podonoghue/T962a_Oven_Controller/Software/SMT_Oven_stubs/Project_Headers/USBDM_Documentation.h

/**
 * @file     USBDM_Documentation.h (180.ARM_Peripherals/Project_Headers/USBDM_Documentation.h)
 * @brief    USBDM Documentation
 */
 
 /**
 @mainpage USBDM Overview

 The classes in the USBDM namespace provide C++ wrappers for the microcontroller hardware. \n

\tableofcontents
Table of Contents
 - \ref ADCExamples \n
 - \ref Console \n
 - \ref DMAExamples \n
 - \ref FTMExamples \n
 - \ref GPIOExamples \n
 - \ref I2CExamples \n
 - \ref LPTMRExamples \n
 - \ref PDBExamples \n
 - \ref PinSummary  \n
 - \ref PITExamples \n
 - \ref SPIExamples \n

@page I2CExamples  I2C interface

Convenience template for SPI. Uses the following classes:\n
<ul>
<li>USBDM::I2cBase_T < Info >
<li>USBDM::I2c
<ul>
<li>USBDM::I2c0
<li>USBDM::I2c1
</ul>
</ul>

<b>Examples</b>\n
 - @ref i2c-example.cpp

@page SPIExamples  SPI interface

Convenience template for SPI. Uses the following classes:\n
<ul>
<li>USBDM::SpiBase_T < Info >
<li>USBDM::Spi
<ul>
<li>USBDM::Spi0
<li>USBDM::Spi1
</ul>
</ul>

<b>Examples</b>\n
 - @ref spi-example.cpp

@page Console  Console and UART interface

Convenience template for UART. Uses the following classes:\n
<ul>
<li>USBDM::Uart_T < Info >
<li>USBDM::UartBuffered_T < Info, rxSize, txSize >
<ul>
<li>USBDM::Console
<li>USBDM::Uart0
<li>USBDM::Uart1
<li>USBDM::Uart2
</ul>
</ul>

<b>Examples</b>\n
 - @ref console-example.cpp

<b>Usage</b>
 @code

   console.writeln("Hello World");

   int value;
   console.write("Enter value: ").readln(value);
   console.write("Value =").writeln(value);

   console<<"Enter value: ">>value<<EndOfLine;
   console<<"Value ="<<value<<EndOfLine;

   // I/O with error checks
   if (console.write("Number: ").readln(integer).isError()) {
      console.writeln("Opps");
   }
   else {
      console.writeln(integer);
   }

   // Utility functions
   Console::ultoa(100, buff);
   console.write("ultoa(100, buff)  = ").writeln(buff);
   Console::ltoa(-100, buff);
   console.write("ltoa(-100, buff)  = ").writeln(buff);

   char *ptr = buff;
   ptr = Console::strcpy(ptr, "Console::ultoa(100, buff) = ");
   ptr = Console::ultoa(100, ptr);
   ptr = Console::strcpy(ptr, ", oh well!");
   console.writeln(buff);
 @endcode

@page DMAExamples  Direct Memory Access Controller

Convenience template for DMAC. Uses the following classes:\n
<ul>
<li>USBDM::DmaTcd \n
<li>USBDM::DmaMux_T < DmaMuxInfo > \n
<li>USBDM::DmaBase_T < DmaInfo > \n
</ul>

This template is an interface for the Direct Memory Access Controller hardware. \n

It provides:\n
- Definitions for channel mappings
- Methods to configure the DMAC and DMAMUX

This is a template class with static methods.\n
<em>It cannot be instantiated.</em>

<b>Examples</b>\n
 - @ref dma-memory-example.cpp
 - @ref dma-memory-template-example.cpp
 - @ref dma-spi-example.cpp
 - @ref dma-uart-example-mk20.cpp
 - @ref dma-uart-example-mk22f.cpp
 - @ref dma-uart-example-mk28f.cpp

 @page GPIOExamples  General Purpose Input Output

@page LPTMRExamples  Low Power Timer

Convenience template for LPTMR. Uses the following classes:\n
<ul>
<li>USBDM::LptmrBase_T < Info > \n
</ul>

This template is an interface for the Low Power Timer hardware. \n

It provides:\n
- Static pin mapping in conjunction with the configuration settings.

This is a template class with static methods.\n
<em>It cannot be instantiated.</em>

<b>Examples</b>\n
 - @ref lptmr-example.cpp
 
 @page GPIOExamples  General Purpose Input Output

Convenience template for GPIO pins. Uses the following classes:\n
<ul>
<li>USBDM::GpioBase_T &lt;clockMask, portAddress, gpioAddress, bitNum, polarity&gt; \n
<li>USBDM::Gpio_T &lt;Info, bitNum, polarity&gt;\n
<ul>
<li>USBDM::GpioA &lt;bitNum, polarity&gt;
<li>USBDM::GpioB &lt;bitNum, polarity&gt;
<li>USBDM::GpioC &lt;bitNum, polarity&gt;
<li>USBDM::GpioD &lt;bitNum, polarity&gt;
<li>USBDM::GpioE &lt;bitNum, polarity&gt;
</ul>
<li>USBDM::Field_T &lt;Info, left, right, polarity&gt;\n
<ul>
<li>USBDM::GpioAField &lt;left, right, polarity&gt;
<li>USBDM::GpioBField &lt;left, right, polarity&gt;
<li>USBDM::GpioCField &lt;left, right, polarity&gt;
<li>USBDM::GpioDField &lt;left, right, polarity&gt;
<li>USBDM::GpioEField &lt;left, right, polarity&gt;
</ul>
</ul>

This template is an interface for the general purpose I/O pin hardware. \n

It provides:\n
- Static pin mapping in conjunction with the configuration settings.
- Setting pin characteristics e.g. pull-ups, drive strength etc
- Changing the pin direction
- Setting outputs to high or low level
- Polling input value
- Polarity (\ref USBDM::ActiveHigh or \ref USBDM::ActiveLow) is selected when instantiated

This is a template class with static methods.\n
<em>It cannot be instantiated.</em>

<b>Examples</b>\n
 - @ref digital-example1.cpp
 - @ref digital-example2.cpp

<b>Usage</b>
 @code
   // Open USBDM namespace.
   // This allows access to USBDM classes and methods without the USBDM:: prefix.
   using namespace USBDM;

   // Temporary for input values
   bool x;

   // Use pin 3 of PORTC as active-high GPIO i.e. PTC3
   using Gpio = GpioC<3, ActiveHigh>;

   // Set as digital output
   Gpio::setOutput();
   // or for more detailed control
   Gpio::setOutput(PinDriveStrength_High, PinDriveMode_OpenDrain);

   // Set pin to active level (polarity is applied)
   Gpio::setActive();
   // or
   Gpio::on();

   // Clear pin to inactive level (polarity is applied)
   Gpio::setInactive();
   // or
   Gpio::off();

   // Set pin to a high level (polarity is ignored)
   Gpio::set();
   // or
   Gpio::high();

   // Set pin to a low level (polarity is ignored)
   Gpio::clear();
   // or
   Gpio::low();

   // Toggle pin
   Gpio::toggle();

   // Set pin to boolean value (polarity is applied)
   Gpio::write(true);

   // Set pin to boolean value (polarity is applied)
   Gpio::write(false);

   // Enable pull-up
   // This will only have effect when pin is an input
   Gpio::setPullDevice(PinPull_Up);

   // Set drive strength
   Gpio::setDriveStrength(PinDriveStrength_High);

   // Set open-drain
   Gpio::setDriveMode(PinDriveMode_OpenDrain);

   // Read pin as boolean value (polarity is applied)
   x = Gpio::read();

   // Read _state_ of pin drive as boolean value (polarity is applied)
   // This may differ from the value on the pin
   // May be useful if the pin is open-drain
   Gpio::setDriveMode(PinOpenDrain);
   Gpio::high();
   if (Gpio::readState() != Gpio::read()) {
      console.writeln("Open-drain pin is being held low");
   }

   // Dynamically change pin to input
   Gpio::setIn();

   // Read pin as boolean value (polarity is applied)
   x = Gpio::read();

   // Read pin as boolean value (polarity is ignored)
   x = Gpio::isHigh();

   // Read pin as boolean value (polarity is ignored)
   x = Gpio::isLow();
 @endcode

@page ADCExamples Analogue-to-Digital

Convenience template for ADC inputs. Use the following classes:\n
<ul>
<li>USBDM::AdcBase_T
<ul>
<li>USBDM::Adc0
<li>USBDM::Adc1
</ul>
<li>USBDM::AdcChannel_T
<ul>
<li>USBDM::Adc0Channel
<li>USBDM::Adc1Channel
</ul>
<li>USBDM::AdcDiffChannel_T
<ul>
<li>USBDM::Adc0DiffChannel
<li>USBDM::Adc1DiffChannel
</ul>
</ul>
This template is an interface for the ADC input pins. \n

It provides:\n
- Static pin mapping in conjunction with the configuration settings. (Some ADC pins have fixed mapping.)
- Setting the resolution in bits
- Setting the conversion parameters e.g. averaging
- Clock and conversion speed are done through the configuration.
- Interrupt driven operation is also supported through a callback if enabled in the configuration.

This is a template class with static methods.\n
<em>It cannot be instantiated.</em>

<b>Examples</b>\n
 - @ref analogue-comparison-example.cpp
 - @ref analogue-diff-example.cpp
 - @ref analogue-interrupt-example.cpp
 - @ref analogue-joystick-example.cpp

 <b>Usage - Single-ended measurement</b>
 @code
   // Open USBDM namespace.
   // This allows access to USBDM classes and methods without the USBDM:: prefix.
   using namespace USBDM;

   // ADC being used (for shared settings)
   using Adc         = Adc0;

   // Use ADC0 channel 6 as ADC input (ADC_IN6)
   using AdcChannel = USBDM::Adc0Channel<6>;

   // Initially configure ADC for resolution of 16 bits with default settings
   Adc::configure(AdcResolution_16bit_se);

   // Calibrate before use
   Adc::calibrate();
   
   // Set ADC averaging to 4 samples
   Adc::setAveraging(AdcAveraging_4);

   // Read ADC value
   uint32_t value = AdcChannel::readAnalogue();

   console.write("ADC measurement = ").writeln(value);
 @endcode

 <b>Usage - Differential measurement</b>
 @code
   // Open USBDM namespace.
   // This allows access to USBDM classes and methods without the USBDM:: prefix.
   using namespace USBDM;

   // ADC being used (for shared settings)
   using Adc         = Adc0;

   // Use channel 0 as ADC differential input (ADC_DM0, ADC_DP0)
   using Adc1_diff0 = USBDM::Adc0DiffChannel<0>;

   // Initially configure ADC for resolution of 11 bits differential with default settings
   Adc::configure(AdcResolution_11bit_diff);

   // Calibrate before use
   Adc::calibrate();
   
   // Set ADC averaging to 4 samples
   Adc::setAveraging(AdcAveraging_4);

   // Read signed differential ADC value
   int32_t value = Adc1_diff0::readAnalogue();

   console.write("ADC measurement = ").writeln(value);
 @endcode

@page FTMExamples Flexible Timer Module

Convenience template for FTM hardware.
The interface is divided into a number of templates:
<ul>
<li>USBDM::FtmBase_T Representing the shared FTM functionality.
<ul>
<li>USBDM::Ftm0
<li>USBDM::Ftm1
</ul>
<li>USBDM::QuadEncoder_T Representing a FTM operating as a quadrature encoder.
<ul>
<li>USBDM::QuadEncoder1
</ul>
<li>USBDM::FtmChannel_T Representing individual channels of a single FTM.
<ul>
<li>USBDM::Ftm0Channel
<li>USBDM::Ftm1Channel
</ul>
</ul>
It provides:\n
<ul>
<li>Static pin mapping in conjunction with the configuration settings.
<li>Setting the FTM period in ticks or seconds
<li>Setting the channel duty cycle in percentage
<li>Interrupt driven operation is also supported through a callback if <b>enabled in the configuration</b>.
</ul>

This is a template class with static methods.\n
<em>It cannot be instantiated.</em>

<b>Examples</b>\n
 - @ref ftm-ic-example.cpp
 - @ref ftm-oc-example.cpp
 - @ref ftm-pwm-example.cpp
 - @ref ftm-quadrature-example.cpp
 - @ref ftm-servo-example.cpp

 <b>Usage - PWM</b>
@code
   // Open USBDM namespace.
   // This allows access to USBDM classes and methods without the USBDM:: prefix.
   using namespace USBDM;

   // Initialise the timer with initial alignment
   // This affects all channels of the FTM
   Ftm0::configure(FtmMode_LeftAlign);

   // Set timer period in ticks
   // This affects all channels of the FTM
   // Timer pre-scaler is not changed
   Ftm0::setPeriodInTicks(500);

   // Set timer period in microseconds
   // This affects all channels of the FTM
   // Timer pre-scaler (tick rate) will be adjusted to accommodate the required period
   Ftm0::setPeriod(125*us);

   // Use FTM0 channel 3
   using PwmOutput = Ftm0Channel<3> ;

   // Set channel to generate PWM with active-high pulses
   PwmOutput::enable(ftm_pwmHighTruePulses);

   // Set duty cycle as percentage
   PwmOutput::setDutyCycle(34);

   // Set duty cycle as percentage (float)
   PwmOutput::setDutyCycle(12.25*percent);

   // Set high time in microseconds (float)
   PwmOutput::setHighTime(63*us);
@endcode

 <b>Usage - Quadrature Encoder</b>
@code
   // Open USBDM namespace.
   // This allows access to USBDM classes and methods without the USBDM:: prefix.
   using namespace USBDM;

   // Use FTM1 as the quadrature encoder
   // Not all FTMs support this mode
   using QuadEncoder = QuadEncoder1;

   // Enable encoder
   QuadEncoder::enable();

   // Set pin filters
   QuadEncoder::enableFilter(15);

   // Reset position to zero
   // Movement will be relative to this position
   QuadEncoder::resetPosition();

   // Set up callback for quadrature overflow or underflow
   QuadEncoder::setTimerOverflowCallback(callBack);
   QuadEncoder::enableTimerOverflowInterrupts();
   QuadEncoder::enableNvicInterrupts();

   for (;;) {
      // Report position
      console.write("Shaft position = ").writeln(QuadEncoder::getPosition());
   }
@endcode

@page PITExamples Programmable Interrupt Timer Module

Convenience template for PIT hardware. \n
Uses the following classes:
<ul>
<li> USBDM::PitBase_T &lt;Info&gt;
<li> USBDM::Pit
<li> USBDM::PitChannel &lt;channel&gt;
</ul>
It provides:\n
- Static pin mapping in conjunction with the configuration settings.
- Setting the PIT channel period in seconds
- Accurate busy-wait delays using a timer channel
- Interrupt driven operation is also supported through a callback if enabled in the configuration.

This is a template class with static methods.\n
<em>It cannot be instantiated.</em>

<b>Examples</b>\n
 - @ref pit-example1.cpp
 - @ref pit-example2.cpp
 - @ref pit-example3.cpp

<b>Usage - PIT busy-wait</b>
@code
   // Open USBDM namespace.
   // This allows access to USBDM classes and methods without the USBDM:: prefix.
   using namespace USBDM;

   // LED is assumed active-low
   using Led = GpioA<2, ActiveLow>;

   // Use high drive for LED
   Led::setOutput(pcrValue(PinPull_None, PinDrive_High));

   // Enable PIT
   Pit::enable();

   // Check for errors so far
   checkError();

   for(;;) {
      Led::toggle();

      // Delay in milliseconds using channel 0
      Pit::delay(0, 1000*ms);
   }
@endcode

@page PDBExamples Programmable Delay Block Module

Convenience template for PDB hardware. Based on USBDM::PdbBase_T.\n

It provides:\n
- PDB configuration

This is a template class with static methods.\n
<em>It cannot be instantiated.</em>

<b>Examples</b>\n
 - @ref pdb-example.cpp

<b>Usage - PDB Software Trigger</b>
@code
   // Open USBDM namespace.
   // This allows access to USBDM classes and methods without the USBDM:: prefix.
   using namespace USBDM;

   Pdb::enable();
   // Trigger from FTM
   Pdb::setTriggerSource(PdbTrigger_Software);
   // Set callback
   Pdb::setCallback(pdbCallback);
   // Interrupt during sequence
   Pdb::enableSequenceInterrupts();
   // Set period a bit longer than FTM period
   Pdb::setPeriod(PERIOD);
   // Generate interrupt near end of sequence
   Pdb::setInterruptDelay(PERIOD-5*ms);
   // Take ADC samples before and after sample edge
   Pdb::setPretriggers(0, PdbPretrigger0_Delayed, HIGH_TIME-SAMPLE_DELAY, PdbPretrigger1_Delayed, HIGH_TIME+SAMPLE_DELAY);
   // Update registers
   Pdb::triggerRegisterLoad(PdbLoadMode_immediate);

   Pdb::enableNvicInterrupts();

   Pdb::softwareTrigger();
@endcode

@page Notes Notes
  - enable()            Enables clock and configures pins (if any configured in Configure.usbdmProject)
  - configureAllPins()  Configures all pins associated with the peripheral
  - defaultConfigure()  enable() + initialises according to Configure.usbdmProject\n
                        May have defaulted parameters to do custom configuration.
  - disable()           Disables the peripheral

@example analogue-comparison-example.cpp
@example analogue-diff-example.cpp
@example analogue-interrupt-example.cpp
@example analogue-joystick-example.cpp
@example cmp-example.cpp
@example console-example.cpp
@example dac-example.cpp
@example digital-example1.cpp
@example digital-example2.cpp
@example dma-memory-example.cpp
@example dma-memory-template-example.cpp
@example dma-spi-example.cpp
@example dma-uart-example-mk20.cpp
@example dma-uart-example-mk22f.cpp
@example dma-uart-example-mk28f.cpp
@example flash_programming_example.cpp
@example ftm-ic-example.cpp
@example ftm-oc-example.cpp
@example ftm-pwm-example.cpp
@example ftm-quadrature-example.cpp
@example ftm-servo-example.cpp
@example fxos8700cq-example.cpp
@example fxos8700cq.cpp
@example fxos8700cq.h
@example hmc5883l-example.cpp
@example hmc5883l.cpp
@example hmc5883l.h
@example i2c-example.cpp
@example llwu-example-mk20.cpp
@example llwu-example-mk22f.cpp
@example lptmr-example.cpp
@example mag3310-example.cpp
@example mag3310.cpp
@example mag3310.h
@example mma845x-example.cpp
@example mma845x.cpp
@example mma845x.h
@example mma8491q-example.cpp
@example mma8491q.cpp
@example mma8491q.h
@example nonvolatile_example.cpp
@example pca9685-example.cpp
@example pca9685.cpp
@example pca9685.h
@example pit-example1.cpp
@example pit-example2.cpp
@example pit-example3.cpp
@example pdb-example.cpp
@example rtc-example.cpp
@example spi-example.cpp
@example mcg-test.cpp
@example tsi-mk-example.cpp
@example usb.cpp
@example usb_cdc_interface.cpp
@example usb_cdc_interface.h
@example usb_implementation.h
@example usb_implementation_bulk.cpp
@example usb_implementation_bulk.h
@example usb_implementation_cdc.cpp
@example usb_implementation_cdc.h
@example usb_implementation_composite.cpp
@example usb_implementation_composite.h

 */
