podonoghue/T962a_Oven_Controller/Software/SMT_Oven_RTOS/Project_Headers/cmsis.h

/**
 * @file cmsis.h (180.ARM_Peripherals/Project_Headers/cmsis.h)
 *
 *  Created on: 20Feb.,2017
 *      Author: podonoghue
 */
#ifndef INCLUDE_USBDM_CMSIS_H_
#define INCLUDE_USBDM_CMSIS_H_

#include <cmath>
#include "cmsis_os.h"
#include "error.h"

/**
 * Namespace enclosing wrapper classes for CMSIS-RTX
 */
namespace CMSIS {

/**
 * Set error code
 *
 * @param[in]  err Error code to set
 *
 * @return Error code
 */
inline static USBDM::ErrorCode setCmsisErrorCode(int err) {
   if (err != 0) {
      // Bump error CMSIS error code to avoid conflict with USBDM error codes
      err |= USBDM::E_CMSIS_ERR_OFFSET;
   }
   USBDM::errorCode = (USBDM::ErrorCode)err;
   return USBDM::errorCode;
}

/**
 * Set error code and check for error
 *
 * @param[in]  err Error code to set
 *
 * @return Error code
 */
inline static USBDM::ErrorCode setAndCheckCmsisErrorCode(int err) {
   if (err != 0) {
      // Bump error CMSIS error code to avoid conflict with USBDM error codes
      err |= USBDM::E_CMSIS_ERR_OFFSET;
   }
   USBDM::errorCode = (USBDM::ErrorCode)(err);
   return USBDM::checkError();
}

using Callback = void (*)(const void *);

/**
 * Wrapper for CMSIS Timer
 *
 * A timer allows the scheduling of the execution of a callback function after a particular
 * delay(osTimerOnce mode) or at a regular interval (osTimerPeriodic mode).
 *
 * Example:
 * @code
 * //
 * // Timer example
 * //
 * void timerExample() {
 *    // auto function used as call-backs
 *    static auto cb1 = [] (const void *) {
 *       RED_LED::toggle();
 *    };
 *    static auto cb2 = [] (const void *) {
 *       GREEN_LED::toggle();
 *    };
 *
 *    // Create the two timer being used
 *    static CMSIS::Timer myTimer1(cb1, osTimerPeriodic);
 *    static CMSIS::Timer myTimer2(cb2, osTimerPeriodic);
 *
 *    RED_LED::setOutput();
 *    GREEN_LED::setOutput();
 *
 *    // Start the timers 
 *    myTimer2.start(500);
 *    myTimer1.start(1000);
 *
 *    printf(" myTimer1::getId() = %p\n\r", myTimer1.getId());
 *    printf(" myTimer2::getId() = %p\n\r", myTimer2.getId());
 * }
 * @endcode
 */
class Timer {

private:
   /**
    * Based on os_timer_cb in rt_CMSIS.c
    * Timer Control Block
    */
   struct osTimerControlBlock_t {
      struct os_timer_cb_ *next;   // Pointer to next active Timer
      uint8_t             state;   // Timer State
      uint8_t              type;   // Timer Type (Periodic/One-shot)
      uint16_t         reserved;   // Reserved
      uint32_t             tcnt;   // Timer Delay Count
      uint32_t             icnt;   // Timer Initial Count
      void                 *arg;   // Timer Function Argument
      const osTimerDef_t *timer;   // Pointer to Timer definition
   };

   volatile osTimerControlBlock_t  os_timer_cb  = {0,0,0,0,0,0,0,0};
   const    osTimerDef_t           os_timer_def;

public:
   /**
    * Constructor - Create timer
    *
    * @param[in] callback  Call-back function to execute by timer
    * @param[in] argument  Pointer to data to pass to callback (should be persistent)
    * @param[in] timerType Type of timer e.g. osTimerPeriodic, osTimerOnce
    */
   Timer(Callback callback, void *argument, os_timer_type timerType) :
      os_timer_def{callback, (void*)&os_timer_cb} {
      osTimerId timer_id __attribute__((unused)) = osTimerCreate(&os_timer_def, timerType, argument);
      usbdm_assert((void*)timer_id == (void*)&os_timer_cb, "Internal check failed");
   }
   /**
    * Constructor - Create timer of given type
    *
    * @param[in] callback  Call-back function to execute by timer
    * @param[in] timerType Type of timer e.g. osTimerPeriodic, osTimerOnce
    */
   Timer(Callback callback, os_timer_type timerType) :
      Timer(callback, nullptr, timerType) {
   }
   /**
    * Constructor - Create Periodic timer
    *
    * @param[in] callback  Call-back function to execute by timer
    * @param[in] argument  Pointer to data to pass to callback (should be persistent)
    */
   Timer(Callback callback, void *argument=nullptr) :
      Timer(callback, argument, osTimerPeriodic){
   }
   /**
    * Destructor
    */
   ~Timer() {
      if (os_timer_cb.state != 0) {
         destroy();
      }
   }
   /**
    * Recreate the associated CMSIS timer with different characteristics
    *
    * @param[in] argument  Pointer to data to pass to callback (should be persistent)
    * @param[in] timerType Type of timer e.g. osTimerPeriodic, osTimerOnce
    *
    * @return true  Success
    * @return false Failure
    */
   bool create(void *argument=nullptr, os_timer_type timerType=osTimerPeriodic) {
      if (os_timer_cb.state != 0) {
         osStatus rc = destroy();
         if (rc != osOK) {
            return rc;
         }
      }
      osTimerId timer_id = osTimerCreate(&os_timer_def, timerType, argument);
      return ((void*)timer_id == (void*)&os_timer_cb);
   }
   /**
    * Destroy the associated CMSIS timer
    *
    * @return error code:
    * @return - osOK:              The timer has been deleted.
    * @return - osErrorISR:        Cannot be called from interrupt service routines.
    * @return - osErrorParameter:  Parameter is incorrect
    */
   osStatus destroy() {
      return osTimerDelete((osTimerId)&os_timer_cb);
   }
   /**
    * Stop the timer
    */
   void stop() {
      osTimerStop((osTimerId)&os_timer_cb);
   }
   /**
    * Start or restart timer
    *
    * @param[in] millisec Interval in milliseconds
    */
   void start(int millisec) {
      setAndCheckCmsisErrorCode(osTimerStart((osTimerId)&os_timer_cb, millisec));
   }
   /**
    * Start or restart timer
    *
    * @param[in] interval Interval in seconds
    */
   void start(double interval) {
      start((int)round(interval*1000.0));
   }
   /**
    * Get timer ID
    *
    * @return CMSIS Timer ID
    */
   inline osTimerId getId() {
      return (osTimerId)&os_timer_cb;
   }
};

/**
 * Wrapper for CMSIS Timer.
 *
 * This class incorporates the call-back function.
 *
 * @tparam timerType Type of timer e.g. osTimerPeriodic, osTimerOnce
 *
 * <b>Example declaration</b>
 * @code
 *  //
 *  // Thread class incorporating thread function
 *  //
 *  class MyTimer : public CMSIS::TimerClass {
 *
 *  private:
 *     // Name to use
 *     const char *fName;
 *
 *     //
 *     // Function executed as timer call-back
 *     //
 *     virtual void callback() override {
 *        printf(fName);
 *     }
 *
 *  public:
 *     //
 *     // Constructor
 *     //
 *     // @param[in] Name for timer function to report
 *     //
 *     MyThread(const char *name) : fName(name) {
 *     }
 *  };
 * @endcode
 *
 * <b>Example instantiation and use</b>
 * @code
 *    //
 *    // Create derived thread class instances
 *    //
 *    MyTimer myTimer1("Timer 1");
 *    MyTimer myTimer2("Timer 2");
 *
 *    // Start timers
 *    myTimer1.start(1000);
 *    myTimer2.start(500);
 *
 * @endcode
 */
class TimerClass : Timer {

private:

   /*
    * Derived classes must override this function to implement the thread\n
    * This would usually be an endless loop
    */
   virtual void callback() = 0;

   /**
    * Shim to allow use of a static call-back needed by CMSIS timer
    *
    * @param[in] arg Pointer to TimerClass instance
    *
    * Strictly should be a separate non-member function with C linkage.
    */
   static void shim(const void *arg) {
      TimerClass *This = static_cast<TimerClass *>(const_cast<void *>(arg));
      This->callback();
   }

   // Hide these
   using Timer::create;
   using Timer::destroy;

public:
   using Timer::start;
   using Timer::stop;
   using Timer::getId;

   TimerClass(os_timer_type timerType=osTimerPeriodic) : Timer(shim, this, timerType) {
   }
   virtual ~TimerClass() {
   }
};

/**
 * Wrapper for CMSIS mutex
 *
 * A Mutex can be used to:
 *    - Synchronize the execution of threads
 *    - Protect access to shared resources. (Implement critical region protection).
 *
 * @note Mutex cannot be used in an ISR
 */
class Mutex {

private:
   uint32_t           os_mutex_cb[4] = { 0 };
   const osMutexDef_t os_mutex_def   = {os_mutex_cb};

public:
   /**
    * Create mutex
    */
   Mutex() {
      osMutexId mutex_id __attribute__((unused)) = osMutexCreate(&os_mutex_def);
      usbdm_assert((void*)mutex_id == (void*)os_mutex_cb, "Internal check failed");
   }
   /**
    * Delete mutex
    */
   ~Mutex() {
      osMutexDelete((osMutexId) os_mutex_cb);
   }
   /**
    * Obtain mutex
    *
    * This method may wait until the mutex is available.\n
    * The millisec parameter allow the wait time to be specified.
    *
    * @param[in] millisec How long to wait in milliseconds.\n
    *                     Use osWaitForever for an indefinite wait\n
    *                     Use 0 to immediately fail if the mutex is not available.
    *
    * @return osOK:                    The mutex has been obtained.
    * @return osErrorTimeoutResource:  The mutex could not be obtained in the given time.
    * @return osErrorResource:         The mutex could not be obtained when no timeout was specified.
    * @return osErrorParameter:        The parameter mutex_id is incorrect.
    * @return osErrorISR:              osMutexWait cannot be called from interrupt service routines.
    */
   osStatus wait(uint32_t millisec=osWaitForever) {
      return osMutexWait((osMutexId) os_mutex_cb, millisec);
   }
   /**
    * Release mutex
    *
    * Release the mutex that was obtained with wait().\n
    * Other threads that are currently waiting for this mutex will be put into the READY state.
    *
    * @return osOK:              The mutex has been correctly released.
    * @return osErrorResource:   The mutex was not obtained beforehand.
    * @return osErrorISR:        osMutexRelease cannot be called from interrupt service routines.
    */
   osStatus release() {
      return osMutexRelease((osMutexId) os_mutex_cb);
   }
   /**
    * Obtain mutex\n
    * See @ref wait();
    */
   osStatus lock(uint32_t millisec=osWaitForever) {
      return osMutexWait((osMutexId) os_mutex_cb, millisec);
   }
   /**
    * Try to obtain mutex with immediate fail if unsuccessful.
    *
    * @return osOK:                   The mutex has been obtain.
    * @return osErrorTimeoutResource: The mutex could not be obtained immediately.
    */
   osStatus tryLock() {
      return osMutexWait((osMutexId) os_mutex_cb, 0);
   }
   /**
    * Unlock mutex\n
    * See @ref release()
    */
   osStatus unlock() {
      return osMutexRelease((osMutexId) os_mutex_cb);
   }
   /**
    * Get mutex ID
    *
    * @return CMSIS mutex ID
    */
   osMutexId getID() {
      return (osMutexId) os_mutex_cb;
   }
};
/**
 * Wrapper for CMSIS Semaphore
 */
class Semaphore {

private:
   uint32_t               os_semaphore_cb[2] = { 0 };
   const osSemaphoreDef_t os_semaphore_def   = { os_semaphore_cb };

public:
   /**
    * Create semaphore
    *
    * @param[in] count Number of available resources.
    */
   Semaphore(int32_t count) {
      osSemaphoreId semaphore_id __attribute__((unused)) = osSemaphoreCreate(&os_semaphore_def, count);
      usbdm_assert((void*)semaphore_id == (void*)os_semaphore_cb, "Internal check failed");
   }
   /**
    * Delete semaphore
    */
   ~Semaphore() {
      osSemaphoreDelete((osSemaphoreId)os_semaphore_cb);
   }
   /**
    * Obtain semaphore
    *
    * @param[in] millisec How long to wait in milliseconds. Use osWaitForever for indefinite wait
    *
    * @return Number of available tokens, or -1 in case of incorrect parameters.
    */
   int32_t wait(uint32_t millisec=osWaitForever) {
      int32_t rc = osSemaphoreWait((osSemaphoreId)os_semaphore_cb, millisec);
      usbdm_assert(rc >= 0, "Illegal parameters");
      return rc;
   }
   /**
    * Release semaphore
    */
   void release() {
      osStatus status __attribute__((unused)) = osSemaphoreRelease((osSemaphoreId)os_semaphore_cb);
      usbdm_assert(status == osOK, "Failed semaphore");
   }
   /**
    * Get semaphore ID
    *
    * @return CMSIS semaphore ID
    */
   osSemaphoreId getID() {
      return (osSemaphoreId)os_semaphore_cb;
   }
};

/**
 * Wrapper for CMSIS Memory Allocation Pool
 *
 * This allows a pool of same-size items to be created.\n
 * Items can be allocated and freed from the pool.\n
 * The main purpose is to avoid fragmentation inherent in the usual C allocation methods
 *
 * @tparam T      Type of items in pool
 * @tparam size   Size of pool in items
 *
 * Example:
 * @code
 * //
 * // Memory pools example
 * //
 * void memoryPoolExample() {
 *    struct Data {
 *       int a;
 *       int b;
 *    };
 *
 *    Pool<Data, 10> pool;
 *
 *    printf(" memory pool::getId() = %p\n\r", pool.getId());
 *
 *    Data *ar[30] = {0};
 *    for (unsigned i=0; i<(sizeof(ar)/sizeof(ar[0])); i++) {
 *       ar[i] = pool.alloc();
 *       if (ar[i] == nullptr) {
 *          break;
 *       }
 *       else {
 *          printf("%d: Allocated %p\n\r", i, ar[i]);
 *       }
 *       ar[i]->a = i;
 *       ar[i]->b = i*i;
 *    }
 *    for (unsigned i=0; i<(sizeof(ar)/sizeof(ar[0])); i++) {
 *       if (ar[i] != nullptr) {
 *          printf("%d: free %p (%d, %d)\n\r", i, ar[i], ar[i]->a, ar[i]->b);
 *          pool.free(ar[i]);
 *       }
 *    }
 * }
 * @endcode
 */
template <typename T, size_t size>
class Pool {

private:
   uint32_t pool[3+((sizeof(T)+3)/4)*size] = {0};
   const    osPoolDef_t os_pool_def        = { size, sizeof(T), pool };

public:
   Pool() {
   }
   ~Pool() {
   }

   /**
    * Create pool
    */
   void create() {
      osPoolId pool_id = osPoolCreate(&os_pool_def);
      usbdm_assert((void*)pool_id == (void*)pool, "Internal check failed");
   }
   /**
    * Allocate a memory block from the memory pool.
    *
    * @return Address of the allocated memory block or nullptr in case of no memory available.
    */
   T *alloc() {
      if ((pool[0] == 0)&&(pool[1] == 0)) {
         // Lazy creation
         create();
      }
      return (T*)osPoolAlloc((osPoolId)pool);
   }
   /**
    * Allocate a memory block from the memory pool and initialise to all zeroes.
    *
    * @return Address of the allocated memory block or nullptr in case of no memory available.
    */
   T *calloc() {
      if (pool[0] == 0) {
         // Lazy creation
         create();
      }
      return (T*)osPoolCAlloc((osPoolId)pool);
   }
   /**
    * Return a memory block to a memory pool.
    *
    * @param[in] buffer Address of buffer to return to pool
    *
    * @return osOK:             The memory block is released.
    * @return osErrorValue:     Block does not belong to the memory pool.
    * @return osErrorParameter: A parameter is invalid or outside of a permitted range.
    */
   void free(T *buffer) {
      osStatus status = osPoolFree((osPoolId)pool, buffer);
      usbdm_assert(status == osOK, "Internal check failed");
   }
   /**
    * Get pool ID
    *
    * @return CMSIS pool ID
    */
   osPoolId getId() {
      return (osPoolId)pool;
   }
};

/**
 * Wrapper for CMSIS Thread
 *
 * @code
 * //
 * // Thread example
 * //
 * void threadExample() {
 *    static auto threadFn = [] (const void *) {
 *       for(;;) {
 *          BLUE_LED::toggle();
 *          osDelay(2000);
 *       }
 *    };
 *    static Thread thread(threadFn);
 *
 *    BLUE_LED::setOutput();
 *
 *    thread.run();
 *    printf(" thread::getId() = %p\n\r", thread.getId());
 * }
 * @endcode
 */
class Thread {

private:
   const osThreadDef_t thread_def;
   osThreadId thread_id = 0;

public:
   /**
    * Run thread
    *
    * @param[in] argument Argument to thread function
    */
   void run(void *argument=nullptr) {
      thread_id = osThreadCreate(&thread_def, argument);
      setAndCheckCmsisErrorCode((thread_id != nullptr)?osOK:osErrorOS);
   }
   /**
    * Get thread ID
    *
    * @return ID of thread
    */
   osThreadId getId() {
      return thread_id;
   }
   /**
    * Get thread ID of current thread
    *
    * @return ID of thread
    */
   static osThreadId getMyId() {
      return osThreadGetId();
   }
   /**
    * Get thread Priority
    *
    * @return Priority of thread
    */
   osPriority getPriority() {
      return osThreadGetPriority(thread_id);
   }
   /**
    * Get priority of current thread
    *
    * @return Priority of thread
    */
   static osPriority getMyPriority() {
      auto threadId = CMSIS::Thread::getMyId();
      return osThreadGetPriority(threadId);
   }
   /**
    * Get thread Priority
    *
    * @param[in] threadId Thread ID of thread to adjust priority of
    *
    * @return Priority of thread
    */
   static osPriority getPriority(osThreadId threadId) {
      return osThreadGetPriority(threadId);
   }
   /**
    * Set thread Priority
    *
    * @param[in] priority Priority to set for thread
    *
    * @return osOK:              The priority of the thread has been successfully changed.
    * @return osErrorValue:      Incorrect priority value.
    * @return osErrorResource:   Thread that is not an active thread.
    * @return osErrorISR:        Cannot be called from interrupt service routines.
    */
   osStatus setPriority(osPriority priority) {
      return osThreadSetPriority(thread_id, priority);
   }

   /**
    * Set thread Priority
    *
    * @param[in] threadId Thread ID of thread to adjust priority of
    * @param[in] priority Priority to set for thread
    *
    * @return osOK:              The priority of the thread has been successfully changed.
    * @return osErrorValue:      Incorrect priority value.
    * @return osErrorResource:   Thread that is not an active thread.
    * @return osErrorISR:        Cannot be called from interrupt service routines.
    */
   static osStatus setPriority(osThreadId threadId, osPriority osPriority) {
      return osThreadSetPriority(threadId, osPriority);
   }

   /**
    * Set priority of current thread
    *
    * @param[in] priority Priority to set for thread
    *
    * @return osOK:              The priority of the thread has been successfully changed.
    * @return osErrorValue:      Incorrect priority value.
    * @return osErrorResource:   Thread that is not an active thread.
    * @return osErrorISR:        Cannot be called from interrupt service routines.
    */
   static osStatus setMyPriority(osPriority osPriority) {
      auto threadId = CMSIS::Thread::getMyId();
      return osThreadSetPriority(threadId, osPriority);
   }

   /**
    * Pass control to the next thread that is in state READY.
    * If there is no other thread in the state READY, the current
    * thread continues execution and no thread switching occurs.
    *
    * @return osOK:       The function has been correctly executed.
    * @return osErrorISR: Cannot be called from interrupt service routines.
    *
    */
   static osStatus yield() {
      return osThreadYield();
   }
   /**
    * Set the specified Signal Flags on the thread
    *
    * @param[in] signals Specifies the signal flags of the thread that should be set.
    *
    * @return Previous signal flags of the specified thread or 0x80000000 in case of incorrect parameters or call from ISR.
    *
    */
   int32_t signalSet(int32_t signals) {
      return osSignalSet(thread_id, signals);
   }
   /**
    * Clear the specified Signal Flags on the thread
    *
    * @param[in] signals Specifies the signal flags of the thread that shall be cleared.
    *
    * @return Previous signal flags of the specified thread or 0x80000000 in case of incorrect parameters or call from ISR.
    */
   int32_t signalClear(int32_t signals) {
      return osSignalClear(thread_id, signals);
   }
   /**
    * Wait for one or more Signal Flags to become signaled for the current thread.
    *
    * @param[in] signals  Wait until all specified signal flags set or 0 for any single signal flag.
    * @param[in] millisec How long to wait in milliseconds. Use osWaitForever for indefinite wait
    *
    * @return Structure describing event occurring with status:
    * @return - osOK: no signal received when the timeout value millisec was 0.
    * @return - osEventTimeout: signal not occurred within timeout
    * @return - osEventSignal: signal occurred, value.signals contains the signal flags; these signal flags are cleared.
    * @return - osErrorValue: the value signals is outside of the permitted range.
    * @return - osErrorISR: osSignalWait cannot be called from interrupt service routines.
    *
    */
   static osEvent signalWait(int32_t signals, uint32_t millisec=osWaitForever) {
      return osSignalWait(signals, millisec);
   }
   /**
    * Terminate the thread.
    *
    * @return - osOK: the specified thread has been successfully terminated.
    * @return - osErrorParameter: thread_id is incorrect.
    * @return - osErrorResource: thread_id refers to a thread that is not an active thread.
    * @return - osErrorISR: osThreadTerminate cannot be called from interrupt service routines.
    */
   osStatus terminate() {
      return osThreadTerminate(thread_id);
   }

#if (osFeature_Wait != 0)
   /**
    * Wait for any event of the type Signal, Message, Mail for a specified time period.
    * While the system waits the thread that is calling this function is put into the state WAITING. When millisec is set to osWaitForever the function will wait for an infinite time until a event occurs.
    *
    * @param[in] millisec How long to wait in milliseconds. Use osWaitForever for indefinite wait.
    *
    * @return Status with:
    * @return osEventSignal:  Signal event occurred and is returned.
    * @return osEventMessage: Message event occurred and is returned.
    * @return osEventMail:    Mail event occurred and is returned.
    * @return osEventTimeout: Time delay is executed.
    * @return osErrorISR:     Cannot be called from interrupt service routines.
    */
   static osStatus wait(uint32_t millisec) {
      return osWait(millisec);
   }
#endif

   /**
    * Wait for a specified time period in milliseconds.
    *
    * @param[in] millisec How long to wait in milliseconds. Use osWaitForever for indefinite wait.
    *
    * @return Status with:
    * @return osEventTimeout:  The time delay is executed.
    * @return osErrorISR:      Cannot be called from interrupt service routines.
    */
   static osStatus delay(uint32_t millisec) {
      return osDelay(millisec);
   }
   /**
    * Create thread as a wrapper for an existing thread
    *
    * @param[in] thread_id   ID of existing thread
    */
   Thread(osThreadId thread_id) : thread_def{0, osPriorityNormal, 1, 0}, thread_id(thread_id) {
   };
   /**
    * Create thread
    *
    * @param[in] threadFunction   Function to execute as the thread
    * @param[in] priority         Priority of thread e.g. osPriorityNormal
    * @param[in] stackSize        Stack size for thread or 0 to indicate default
    */
   Thread(
         Callback    threadFunction,
         osPriority  priority=osPriorityNormal,
         uint32_t    stackSize=0) : thread_def {threadFunction, priority, 1, stackSize} {
         };
         /**
          * Delete thread
          */
         ~Thread() {
            osThreadTerminate(thread_id);
         }
};

/**
 * Wrapper for CMSIS Thread.
 *
 * This class incorporates the thread function.
 *
 * <b>Example declaration</b>
 * @code
 *  //
 *  // Thread class incorporating thread function
 *  //
 *  class MyThread : public CMSIS::ThreadClass {
 *
 *  private:
 *     // Name to use
 *     const char *fName;
 *
 *     //
 *     // Function executed as thread
 *     //
 *     virtual void task() override {
 *        for(;;) {
 *           printf(fName);
 *           CMSIS::Thread::delay(300);
 *        }
 *     }
 *
 *  public:
 *     //
 *     // Constructor
 *     //
 *     // @param[in] Name for thread function to report
 *     //
 *     MyThread(const char *name) : fName(name) {
 *     }
 *  };
 * @endcode
 *
 * <b>Example instantiation and use</b>
 * @code
 *    //
 *    // Create derived thread class instances
 *    //
 *    MyThread thread1("Th 1");
 *    MyThread thread2("Th 2");
 *
 *    // Start threads
 *    thread1.run();
 *    thread2.run();
 * @endcode
 */
class ThreadClass : Thread {

private:
   /*
    * Derived classes must override this function to implement the thread\n
    * This would usually be an endless loop
    */
   virtual void task() = 0;

   /**
    * Shim to allow use of a static call-back
    *
    * @param[in] arg Pointer to ThreadClass instance
    *
    * Strictly should be a separate non-member function with C linkage.
    */
   static void shim(const void *arg) {
      ThreadClass *This = static_cast<ThreadClass *>(const_cast<void *>(arg));
      This->task();
   }

public:
   using Thread::getId;
   using Thread::getMyId;
   using Thread::getPriority;
   using Thread::setPriority;
   using Thread::yield;
   using Thread::signalSet;
   using Thread::signalClear;
   using Thread::signalWait;
   using Thread::terminate;
   using Thread::delay;
#if (osFeature_Wait != 0)
   using Thread::wait;
#endif

   /**
    * Create thread
    *
    * @param[in] priority         Priority of thread e.g. osPriorityNormal
    * @param[in] stackSize        Stack size for thread or 0 to indicate default
    */
   ThreadClass(
         osPriority  priority=osPriorityNormal,
         uint32_t    stackSize=0)
   : Thread(shim, priority, stackSize) {
   }
   virtual ~ThreadClass() {
   }

   void run() {
      Thread::run(this);
   }
};

/**
 * Wrapper for CMSIS Message Queue
 *
 * Basic approach:
 *    - Message queues can buffer a number of items (messages) being transferred.
 *    - Messages can be added or removed from the queue.
 *    - Typically the messages will be a small integral item such as an integer.  Alternatively \n
 *      it could be a pointer to a larger item that is statically or dynamically allocated.
 *      The allocation and deallocation is not handled by the message queue.
 *
 * @tparam T      Type of items in message queue. Must fit in 32-bits\n
 *                This is typically a simple type like a character or integer, or a pointer to
 *                a larger type allocated in some independent fashion.
 * @tparam size   Size of message queue in items
 *
 * Example:
 * @code
 * struct MessageData {
 *    int a;
 *    int b;
 * };
 *
 * static bool messageQueueTestComplete = false;
 *
 * static CMSIS::MessageQueue<MessageData*, 10> messageQueue;
 *
 * void messageQueueSender(const void *) {
 *    MessageData ar[30];
 *    for (unsigned i=0; i<(sizeof(ar)/sizeof(ar[0])); i++) {
 *       ar[i].a = i;
 *       ar[i].b = i*i;
 *       printf("%d: Sending %p (%d, %d)\n\r", i, &ar[i], ar[i].a, ar[i].b);
 *       osStatus rc = messageQueue.put(&ar[i], 0);
 *       osDelay(100);
 *       if (rc == osErrorResource) {
 *          break;
 *       }
 *    }
 *    printf("=== Sender complete ====\n\r");
 * }
 *
 * void messageQueueReceiver(const void *) {
 *    for(unsigned i=0; ; i++) {
 *       osEvent event = messageQueue.get(10000);
 *       if (event.status != osEventMessage) {
 *          break;
 *       }
 *       MessageData *data = messageQueue.getValueFromEvent(event);
 *       printf("%d: Received %p (%d, %d)\n\r", i, data, data->a, data->b);
 *    }
 *    messageQueueTestComplete = true;
 *    printf("=== Receiver complete ====\n\r");
 * }
 *
 * //
 * // Message Queue example
 * //
 * void messageQueueExample() {
 *    printf(" message messageQueue.getId() = %p\n\r", messageQueue.getId());
 *
 *    messageQueue.create();
 *    Thread sender(messageQueueSender);
 *    Thread receiver(messageQueueReceiver);
 *
 *    receiver.run();
 *    sender.run();
 *
 *    while(!messageQueueTestComplete) {
 *       __asm__("nop");
 *    }
 * }
 * @endcode
 */
template <typename T, size_t size, Thread *thread=nullptr>
class MessageQueue {

   static_assert(sizeof(T)<=sizeof(int), "Object is too large to pass as message");

private:
   uint32_t              queue[4+size] = {0};
   const osMessageQDef_t os_pool_def   = { size, queue };

   //   static void *operator new     (size_t) = delete;
   //   static void *operator new[]   (size_t) = delete;
   //   static void  operator delete  (void*)  = delete;
   //   static void  operator delete[](void*)  = delete;

public:
   MessageQueue() {
   }

   ~MessageQueue() {
   }
   /**
    * Create message queue
    *
    * @return osMessageQId or NULL if failed.
    */
   osMessageQId create() {
      osThreadId threadId = 0;
      if (thread != 0) {
         threadId = thread->getId();
      }
      osMessageQId message_id = osMessageCreate(&os_pool_def, threadId);
      usbdm_assert((void*)message_id == (void*)queue, "Internal check failed");
      return message_id;
   }
   /**
    * Put message to queue.
    * Returns immediately (for use in ISRs)
    *
    * @param[in] info     Message to send
    *
    * @return osOK: the message is put into the queue.
    * @return osErrorResource: no memory in the queue was available.
    * @return osErrorParameter: a parameter is invalid or outside of a permitted range.
    */
   osStatus putISR(T info) {
      return osMessagePut((osMessageQId)queue, (uint32_t)info, 0);
   }
   /**
    * Put message to queue with timeout
    *
    * @param[in] info     Message to enter
    * @param[in] millisec How long to wait in milliseconds. Use osWaitForever for indefinite wait
    *
    * @return osOK: the message is put into the queue.
    * @return osErrorResource: no memory in the queue was available.
    * @return osErrorTimeoutResource: no memory in the queue was available during the given time limit.
    * @return osErrorParameter: a parameter is invalid or outside of a permitted range.
    */
   osStatus put(T info, uint32_t millisec=osWaitForever) {
      if ((queue[0]==0) && (queue[1]==0)) {
         create();
      }
      return osMessagePut((osMessageQId)queue, (uint32_t)info, millisec);
   }
   /**
    * Get message from queue.
    *
    * @param[in] millisec How long to wait in milliseconds. Use osWaitForever for indefinite wait
    *
    * @return Status and Error Codes
    * @return osOK: no message is available in the queue and no timeout was specified.
    * @return osEventTimeout: no message has arrived during the given timeout period.
    * @return osEventMessage: message received, value.p contains the pointer to message.
    * @return osErrorParameter: a parameter is invalid or outside of a permitted range.
    */
   osEvent get(uint32_t millisec=osWaitForever) {
      if ((queue[0]==0) && (queue[1]==0)) {
         create();
      }
      return osMessageGet((osMessageQId)queue, millisec);
   }
   /**
    * Obtains object contained in event.
    *
    * @param event Event to use.  Usually obtained from get().
    *
    * @return Object from event
    */
   static T getValueFromEvent(osEvent event) {
      return (T)(event.value.p);
   }

   /**
    * Get message from queue.
    * Returns immediately (for use in ISRs)
    *
    * @return Status and Error Codes
    * @return osOK: no message is available in the queue.
    * @return osEventMessage: message received, value.p contains the pointer to message.
    * @return osErrorParameter: a parameter is invalid or outside of a permitted range.
    */
   osEvent getISR() {
      osEvent event = osMessageGet((osMessageQId)queue, 0);
      usbdm_assert (event.status != osErrorParameter, "Internal check failed");
      return event;
   }
   /**
    * Get pool ID
    *
    * @return CMSIS pool ID
    */
   osMessageQId getId() {
      return (osMessageQId)queue;
   }
};

/**
 * Wrapper for CMSIS MailQueue queue
 *
 * Basic approach:
 *    - Mail queues work in conjunction with a <b>pool</b> of <b>messages</b>.
 *    - Messages are <b>allocated</b> from the pool and added to the mail queue.
 *    - Messages are then removed from the mail queue and <b>freed</b> after use.
 *
 * @tparam T           Type of items in mail queue (determines size of items in pool)
 * @tparam queueSize   Size of mail queue in items (determines number of items that can be allocated from the pool)
 *
 * Example:
 * @code
 * struct MailData {
 *    int a;
 *    int b;
 * };
 *
 * static bool mailQueueTestComplete = false;
 *
 * static MailQueue<MailData, 10> mailQueue;
 *
 * void mailQueueSender(const void *) {
 *    for (unsigned i=0; i<20; i++) {
 *       MailData *data = mailQueue.alloc(0);
 *       if (data == nullptr) {
 *          break;
 *       }
 *       printf("%d: Allocated %p\n\r", i, data);
 *       data->a = i;
 *       data->b = i*i;
 *       printf("%d: Sending   %p (%d, %d)\n\r", i, &data, data->a, data->b);
 *       mailQueue.put(data);
 *       osDelay(100);
 *    }
 *    printf("=== Sender complete ====\n\r");
 *    while(!mailQueueTestComplete) {
 *       __asm__("nop");
 *    }
 * }
 *
 * void mailQueueReceiver(const void *) {
 *    for(unsigned i=0; ; i++) {
 *       osEvent event = mailQueue.get(5000);
 *       if (event.status != osEventMail) {
 *          break;
 *       }
 *       MailData *data = messageQueue.getValueFromEvent(event);
 *       printf("%d: Received  %p (%d, %d)\n\r", i, data, data->a, data->b);
 *       mailQueue.free(data);
 *    }
 *    mailQueueTestComplete = true;
 *    printf("=== Receiver complete ====\n\r");
 * }
 *
 * //
 * // Mail queue example
 * //
 * void mailQueueExample() {
 *
 *    printf(" mail mailQueue.getId() = %p\n\r", mailQueue.getId());
 *
 *    mailQueue.create();
 *
 *    Thread sender(mailQueueSender);
 *    Thread receiver(mailQueueReceiver);
 *
 *    receiver.run();
 *    sender.run();
 *
 *    while(!mailQueueTestComplete) {
 *       __asm__("nop");
 *    }
 * }
 * @endcode
 */
template <typename T, size_t queueSize, Thread *thread=nullptr>
class MailQueue {

   struct MainQueue_cb {
      uint8_t     cb_type;          /** Control Block Type                      */
      uint8_t     state;            /** State flag variable                     */
      uint8_t     isr_st;           /** State flag variable for isr functions   */
      void       *p_lnk;            /** Chain of tasks waiting for message      */
      uint16_t    first;            /** Index of the message list begin         */
      uint16_t    last;             /** Index of the message list end           */
      uint16_t    count;            /** Actual number of stored messages        */
      uint16_t    size;             /** Maximum number of stored messages       */
      void        *msg[queueSize];  /** FIFO of Message pointers   */
   };
   struct MessageBuffer {
     void      *free;                                 /** Pointer to first free memory block      */
     void      *end;                                  /** Pointer to memory block end             */
     uint32_t  blk_size;                              /** Memory block size                       */
     uint32_t  messages[((sizeof(T)+3)/4)*queueSize]; /** Message pool*/
   };

private:
   MainQueue_cb         queue;
   MessageBuffer        messages;
   const  void         *pool[2]       = {&queue, &messages};
   const  os_mailQ_def os_mail_def    = {queueSize, sizeof(T), pool};

   //   static void *operator new     (size_t) = delete;
   //   static void *operator new[]   (size_t) = delete;
   //   static void  operator delete  (void*)  = delete;
   //   static void  operator delete[](void*)  = delete;

public:
   bool checkBounds(void *p) {
      return ((p == nullptr) || ((p>=messages.messages) && (p<messages.messages+((sizeof(T)+3)/4)*queueSize)));
   }

   void check() {
      usbdm_assert(checkBounds(messages.free), "Pointer corrupted");
   }

   /**
    * Create mail queue
    */
   void create() {
      osThreadId threadId = 0;
      if (thread != 0) {
         threadId = thread->getId();
      }
      osMailQId queue_id __attribute__((unused)) = osMailCreate(&os_mail_def, threadId);
      usbdm_assert(queue_id == (osMailQId)pool, "Internal check failed");
   }
   /**
    * Allocate a memory block from the mail queue memory pool
    *
    * @param[in] millisec How long to wait in milliseconds. Use osWaitForever for indefinite wait.
    *
    * @return Pointer to allocated block or nullptr on failure.
    */
   T *alloc(uint32_t millisec=osWaitForever) {
      if ((messages.free==nullptr) && (messages.end==nullptr)) {
         create();
      }
      return (T *) osMailAlloc((os_mailQ_cb *)&pool, millisec);
   }

   /**
    * Allocate a memory block from the mail queue\n
    * For use in ISRs.  It will immediately fail if no buffers are available.
    *
    * @return Pointer to allocated block or nullptr on failure.

    * @return osOK: the block has been allocated
    * @return osErrorParameter: a parameter is invalid or outside of a permitted range.
    */
   T *allocISR() {
      return (T *)osMailAlloc((os_mailQ_cb *)&pool, 0);
   }

   /**
    * Allocate a memory block from the mail queue and initialise to all zeroes.
    *
    * @param[in] millisec How long to wait in milliseconds. Use osWaitForever for indefinite wait.
    *
    * @return Pointer to allocated block or nullptr on failure.
    */
   T *calloc(uint32_t millisec=osWaitForever) {
      if ((messages.free == nullptr) && (messages.end == nullptr)) {
         create();
      }
      return (T *)osMailCAlloc((os_mailQ_cb *)&pool, millisec);
   }

   /**
    * Allocate a memory block from the mail queue and initialise to all zeroes.\n
    * For use in ISRs.
    *
    * @param[in] millisec How long to wait in milliseconds. Use osWaitForever for indefinite wait
    *
    * @return Pointer to allocated block or nullptr on failure.
    */
   T *callocISR(uint32_t millisec) {
      return (T *)osMailCAlloc((osMailQId)&pool, 0);
   }

   /**
    * Free a memory block from the mail queue.
    *
    * @param[in] mail Mail block to free (previously allocated with alloc or calloc)
    *
    * @return osOK:              The mail block is released.
    * @return osErrorValue:      Mail block does not belong to the mail queue pool.
    * @return osErrorParameter:  The value to the parameter queue_id is incorrect.
    */
   osStatus free(T *mail) {
      return osMailFree((osMailQId)&pool, mail);
   }

   /**
    * Get a mail item from the mail queue.
    *
    * @param[in] millisec How long to wait in milliseconds. Use osWaitForever for indefinite wait.
    *
    * @return Status with:
    * @return osOK:              No mail is available in the queue and no timeout was specified
    * @return osEventTimeout:    No mail has arrived during the given timeout period.
    * @return osEventMail:       Mail received, value.p contains the pointer to mail content.
    * @return osErrorParameter:  A parameter is invalid or outside of a permitted range.
    */
   osEvent get(uint32_t millisec=osWaitForever) {
      return osMailGet((os_mailQ_cb *)&pool, millisec);
   }

   /**
    * Get a mail item from the mail queue.\n
    * For use in ISRs
    *
    * @return osOK:              No mail is available in the queue
    * @return osEventMail:       Mail received, value.p contains the pointer to mail content.
    * @return osErrorParameter:  A parameter is invalid or outside of a permitted range.
    */
   osEvent getISR() {
      return osMailGet((os_mailQ_cb *)&pool, 0);
   }

   /**
    * Obtains pointer to object indicated by event.
    *
    * @param event Event to use.  Usually obtained from get().
    *
    * @return Object reference
    */
   static T *getValueFromEvent(osEvent event) {
      return (T*)(event.value.p);
   }

   /**
    * Put a mail item into the mail queue.
    *
    * @param[in] mail A mail block previously allocated by alloc() or calloc().
    *
    * @return osOK:              The message is put into the queue.
    * @return osErrorValue:      Mail was previously not allocated as memory slot.
    * @return osErrorParameter:  A parameter is invalid or outside of a permitted range.
    */
   osStatus put(T *mail) {
      return osMailPut((os_mailQ_cb *)&pool, mail);
   }
   /**
    * Get mail queue ID
    *
    * @return CMSIS mail queue ID
    */
   osMailQId getId() {
      return (osMailQId)queue;
   }
};

}; // end namespace CMSIS
#endif /* INCLUDE_USBDM_CMSIS_H_ */
