podonoghue/T962a_Oven_Controller/Software/SMT_Oven_RTOS/Sources/dataPoint.h

/**
 * @file DataPoint.h
 *
 *  Created on: 12Mar.,2017
 *      Author: podonoghue
 */

#ifndef SOURCES_DATAPOINT_H_
#define SOURCES_DATAPOINT_H_

#include <math.h>
#include <stdint.h>
#include "Max31855.h"

/**
 * Mode of operation within profile
 */
enum State {
   s_off,        //!< Off
   s_fail,       //!< Failed
   s_init,       //!< Initialization
   s_preheat,    //!< Preheat
   s_soak,       //!< Soak
   s_ramp_up,    //!< Ramp up
   s_dwell,      //!< Dwell
   s_ramp_down,  //!< Ramp down
   s_complete,   //!< Complete
   s_manual,     //!< Manual
};

/**
 * Represents a data point for plotting etc.
 *
 * To save space 16-bit scaled integers are used internally to represent temperatures.
 * These are scaled to floats on input/output.
 */
class DataPoint {

public:
   using ThermocoupleStatus = Max31855::ThermocoupleStatus;

   static constexpr unsigned NUM_THERMOCOUPLES = 4;

   using TemperatureArray = float[NUM_THERMOCOUPLES];
   using StatusArray      = ThermocoupleStatus[NUM_THERMOCOUPLES];

private:
   /** Value used to scale float to scaled integer values => 2 decimal places */
   static constexpr float FIXED_POINT_SCALE    = 100.0;

   /* Bit encoding for fState_status */
   static constexpr int   THERMO_STATUS_WIDTH  = 3;
   static constexpr int   THERMO_STATUS_MASK   = (1<<THERMO_STATUS_WIDTH)-1;

   /**
    * Union to encode the Profile State and Thermocouple status efficiently for storage.
    */
   union EncodedStatus {
      uint16_t raw;
      struct {
         ThermocoupleStatus th0:3;
         ThermocoupleStatus th1:3;
         ThermocoupleStatus th2:3;
         ThermocoupleStatus th3:3;
         State              state:4;
      };
      constexpr EncodedStatus(uint16_t value) : raw(value) {}
   };

   EncodedStatus fState_status;                  // Controller state and thermocouple status (encoded)

   uint8_t  fHeater;                             // Heater duty cycle
   uint8_t  fFan;                                // Fan duty cycle
   uint16_t fTargetTemp;                         // Oven target temperature (scaled by FIXED_POINT_SCALE)
   uint16_t fThermocouples[NUM_THERMOCOUPLES];   // Thermocouple values

public:
   /**
    * Constructor
    */
   DataPoint() : fState_status{0}, fHeater{0}, fFan{0}, fTargetTemp{0}, fThermocouples{0,0,0,0} {
   }
   /**
    * Get recorded status of a thermocouple
    *
    * @param[in] index Index of thermocouple
    *
    * @return Status
    */
   ThermocoupleStatus getStatus(unsigned index) const {
      return (ThermocoupleStatus)((fState_status.raw>>(THERMO_STATUS_WIDTH*index))&THERMO_STATUS_MASK);
   }

   /**
    * Set recorded status of a thermocouple
    *
    * @param[in] index Index of thermocouple
    * @param[in] status Status to set
    */
   void setStatus(unsigned index, ThermocoupleStatus status) {
      fState_status =
            (fState_status.raw & ~(THERMO_STATUS_MASK<<(THERMO_STATUS_WIDTH*index))) |
            ((status&THERMO_STATUS_MASK)<<(THERMO_STATUS_WIDTH*index));
   }

   /**
    * Get recorded thermocouple temperature
    *
    * @param[in]  index         Index of thermocouple
    * @param[out] temperature   Temperature value
    *
    * @return Status of thermocouple
    */
   ThermocoupleStatus getTemperature(unsigned index, float &temperature) const {
      temperature = fThermocouples[index]/FIXED_POINT_SCALE;
      return getStatus(index);
   }

   /**
    * Set recorded thermocouple temperature
    *
    * @param[in] index       Index of thermocouple
    * @param[in] temperature Temperature to set
    */
   void setTemperature(unsigned index, float temperature) {
      fThermocouples[index] = round(temperature*FIXED_POINT_SCALE);
   }

   /**
    * Calculates the average oven temperature from active recorded thermocouples
    *
    * @return Average value as float or NAN if no thermocouples active
    */
   float getAverageTemperature() const {
      float average   = 0;
      int   numTemps = 0;
      for (unsigned index=0; index<NUM_THERMOCOUPLES; index++) {
         if (getStatus(index) == Max31855::TH_ENABLED) {
            average += fThermocouples[index];
            numTemps++;
         }
      }
      if (numTemps == 0) {
         return NAN;
      }
      return (average/FIXED_POINT_SCALE)/numTemps;
   }

   /**
    * Determine the maximum of recorded thermocouples and recorded target temperature.\n
    * Used for scaling
    *
    * @return Maximum value as float
    */
   float maximum() const {
      uint16_t max = fTargetTemp;
      for (unsigned index=0; index<NUM_THERMOCOUPLES; index++) {
         if (fThermocouples[index]>max) {
            max = fThermocouples[index];
         }
      }
      return max/FIXED_POINT_SCALE;
   }
   /**
    * Records a set of thermocouple values
    *
    * @param[in] thermoCouples  Thermocouple temperature values to record
    * @param[in] status         Status of thermocouple.
    */
   void setThermocouplePoint(TemperatureArray &thermoCouples, StatusArray &status) {
      for (unsigned index=0; index<NUM_THERMOCOUPLES; index++) {
         setTemperature(index, thermoCouples[index]);
         setStatus(index, status[index]);
      }
   }
   /**
    * Get a set of recorded thermocouple values
    *
    * @param[out] thermoCouples   Thermocouple values
    * @param[out] statuses        Statuses of thermocouples.
    */
   void getThermocouplePoint(TemperatureArray &thermoCouples, StatusArray &statuses) const {
      for (unsigned index=0; index<NUM_THERMOCOUPLES; index++) {
         thermoCouples[index]   = fThermocouples[index]/FIXED_POINT_SCALE;
         statuses[index]        = getStatus(index);
      }
   }
   /**
    * Get recorded target temperature
    *
    * @return Target temperature in Celsius
    */
   float getTargetTemperature() const {
      return (fTargetTemp/FIXED_POINT_SCALE);
   }
   /**
    * Record target temperature
    *
    * @param temp Temperature to set
    */
   void setTargetTemperature(float temp) {
      fTargetTemp = round(temp * FIXED_POINT_SCALE);
   }
   /**
    * Get recorded state
    *
    * @return state e.g. s_soak
    */
   State getState() const {
      return fState_status.state;
   }
   /**
    * Record state
    *
    * @param[in] state State e.g. s_soak
    */
   void setState(State state) {
      fState_status.state = state;
   }
   /**
    * Get recorded heater value
    *
    * @return Heater value in percent
    */
   uint8_t getHeater() const {
      return fHeater;
   }
   /**
    * Record heater value
    *
    * @param[in] percent Value for heater in percentage
    */
   void setHeater(uint8_t percent) {
      fHeater = percent;
   }
   /**
    * Get recorded fan value
    *
    * @return Fan value in percent
    */
   uint8_t getFan() const {
      return fFan;
   }
   /**
    * Record fan value
    *
    * @param[in] percent Value for heater in percentage
    */
   void setFan(uint8_t percent) {
      fFan = percent;
   }
};

#endif /* SOURCES_DATAPOINT_H_ */
