podonoghue/T962a_Oven_Controller/Software/SMT_Oven_stubs/Sources/mainMenu.h

/**
 * @file    mainMenu.h
 * @brief   Main menu for Oven
 *
 *  Created on: 9Oct.,2016
 *      Author: podonoghue
 */

#ifndef SOURCES_MAINMENU_H_
#define SOURCES_MAINMENU_H_

namespace MainMenu {

extern void run();

}; // namespace MainMenu

#endif /* SOURCES_MAINMENU_H_ */
