podonoghue/T962a_Oven_Controller/Software/SMT_Oven_RTOS/Sources/configure.cpp

/**
 * @file    configure.cpp
 * @brief   Configuration
 *
 *  Created on: 18 Sep 2016
 *      Author: podonoghue
 */

#include "configure.h"
#include "settings.h"

// Note: Most objects are stateless static objects declared in Configure.h

/** Mutex to protect Interactive and Remote control */
CMSIS::Mutex interactiveMutex;

/** SPI used for LCD and Thermocouples */
USBDM::Spi0 spi;

/** LCD */
LCD_ST7920 lcd{spi, lcd_cs};

/** PWM for heater & oven fan */
ZeroCrossingPwm <Heater, HeaterLed, OvenFan, OvenFanLed, Vmains> ovenControl{fanKickTime};

/** Switch debouncer for front panel buttons */
SwitchDebouncer<F1Button, F2Button, F3Button, F4Button, SButton> buttons{};

/**
 * Set output controlling oven
 *
 * @param[in] dutyCycle Controls the Heater/Fan
 */
void outPutControl(float dutyCycle) {
//   PulseTp tp;
   int heaterDutycycle;
   int fanDutycycle;

   if (dutyCycle>=0) {
      heaterDutycycle = dutyCycle;
      fanDutycycle    = minimumFanSpeed;
   }
   else {
      heaterDutycycle = 0;
      fanDutycycle    = -dutyCycle;
      if (fanDutycycle<minimumFanSpeed) {
         fanDutycycle = minimumFanSpeed;
         heaterDutycycle = 10;
      }
   }
   ovenControl.setHeaterDutycycle(heaterDutycycle);
   ovenControl.setFanDutycycle(fanDutycycle);
}

/**
 * Get oven temperature
 * Averages multiple thermocouple inputs
 *
 * @return Averaged oven temperature
 */
float getTemperature() {
   temperatureSensors.updateMeasurements();
   return temperatureSensors.getLastTemperature();
}

/** PID controller */
Pid_T<getTemperature, outPutControl> pid{pidKp, pidKp, pidKp, pidInterval, -100, 100};

/** Thermocouples */
TemperatureSensors temperatureSensors{};

/** Monitor for case temperature */
CaseTemperatureMonitor<CaseFan> caseTemperatureMonitor{temperatureSensors};
