podonoghue/T962a_Oven_Controller/Software/SMT_Oven_stubs/Snippets/cmsis-cpp-thread.cpp

/**
 ============================================================================
 * @file cmsis-cpp-thread.cpp
 * @brief RTX Thread example program
 *
 *  Created on: 10/6/2016
 *      Author: podonoghue
 ============================================================================
 */
#include <stdio.h>
#include "cmsis.h"                      // CMSIS RTX
#include "hardware.h"                   // Hardware interface

using GREEN_LED   = USBDM::GpioB<0>;

/*
 * Thread example
 */
static void threadExample() {
   /** Thread function */
   static auto threadFn = [] (const void *) {
      for(;;) {
         GREEN_LED::toggle();
         osDelay(2000);
      }
   };
   /** Thread class */
   static CMSIS::Thread thread(threadFn);

   GREEN_LED::setOutput();

   /* Start thread */
   thread.run();

   printf(" thread::getId() = %p\n\r", thread.getId());
}

int main() {
   threadExample();

   for(;;) {
   }
   return 0;
}
