podonoghue/T962a_Oven_Controller/Software/SMT_Oven_stubs/Project_Headers/USBDM_CMSIS_Documentation.h

/**
 * @file     USBDM_CMSIS_Documentation.h (180.ARM_Peripherals/Project_Headers/USBDM_CMSIS_Documentation.h)
 * @brief    USBDM CMSIS Documentation
 */
 
 /**
 @page USBDM CMSIS Interface

 The classes in the CMSIS namespace provide C++ wrappers for CMSIS RTOS.
 
 \tableofcontents
Table of Contents
 - \ref CMSIS::MailQueue  \n
 - \ref CMSIS::MessageQueue \n
 - \ref CMSIS::Mutex \n
 - \ref CMSIS::Pool \n
 - \ref CMSIS::Semaphore \n
 - \ref CMSIS::Thread \n
 - \ref CMSIS::ThreadClass \n
 - \ref CMSIS::Timer \n
 - \ref CMSIS::TimerClass \n
 
@example cmsis-cpp-mailQueue.cpp
@example cmsis-cpp-memoryPool.cpp
@example cmsis-cpp-messageQueue.cpp
@example cmsis-cpp-thread.cpp
@example cmsis-cpp-thread-mma845x.cpp
@example cmsis-cpp-timer.cpp
@example cmsis-cpp-timer-mma845x.cpp
@example cmsis-cpp-pid.h

 */
