podonoghue/T962a_Oven_Controller/Software/SMT_Oven_stubs/Sources/copyProfile.h

/**
 * @file CopyProfile.h
 *
 *  Created on: 17Mar.,2017
 *      Author: podonoghue
 */

#ifndef SOURCES_COPYPROFILE_H_
#define SOURCES_COPYPROFILE_H_

namespace CopyProfile {

/**
 * Run copy profile menu
 */
void run(int index);

}; // end namespace CopyProfile

#endif /* SOURCES_COPYPROFILE_H_ */
