podonoghue/T962a_Oven_Controller/Software/SMT_Oven_stubs/Sources/manageProfiles.h

/**
 * @file ManageProfiles.h
 *
 *  Created on: 17Mar.,2017
 *      Author: podonoghue
 */

#ifndef SOURCES_MANAGEPROFILES_H_
#define SOURCES_MANAGEPROFILES_H_

namespace ManageProfiles {
/**
 * Display profiles for selection or editing
 *
 * On exit the current profile may be changed
 */
void profileMenu();
};

#endif /* SOURCES_MANAGEPROFILES_H_ */
