podonoghue/T962a_Oven_Controller/Software/SMT_Oven_stubs/Snippets/analogue-interrupt-example.cpp

/**
 ============================================================================
 * @file analogue-interrupt-example.cpp
 * @brief Example showing use of a interrupts with an ADC channel
 *
 *  Created on: 10/6/2016
 *      Author: podonoghue
 ============================================================================
 */
#include "hardware.h"

using namespace USBDM;

/*
 * Demonstrates conversion on a single channel with interrupts
 */

// Connection mapping - change as required
// (ch(19) = light sensor on FRDM-K20
using adc        = Adc0;
using adcChannel = Adc0Channel<19>;

/**
 * NOTE:  This is not a sensible approach
 *        Using serial I/O in a ISR is very silly!!!!
 */
void handler(uint32_t value, int) {
   // Start next conversion
   adcChannel::startConversion();
   value = value/10;
   for (uint i=0; i<75; i++) {
      if (i<value) {
         console.write('X');
      }
   }
   console.writeln();
}

int main(void) {
   console.writeln("Starting");

   // Enable and configure ADC
   adc::configure(AdcResolution_8bit_se);

   // Calibrate before use
   adc::calibrate();

   // Note: Setting callback affects all channels on that ADC
   adc::setCallback(handler);

   // Check for error so far
   checkError();

   // Start a conversion
   adcChannel::startConversion();

   for(;;) {
   }
}
