podonoghue/T962a_Oven_Controller/Software/SMT_Oven_RTOS/Project_Headers/utilities.h

/**
 * @file     utilities.h (derived from utilities-mk.h)
 * @brief    Utility Routines
 * @version  V4.12.1.160
 * @date     13 May 2013
 */
#ifndef PROJECT_HEADERS_UTILTIES_H_
#define PROJECT_HEADERS_UTILTIES_H_

#include <stdint.h>

/**
 * @brief Concatenate two tokens
 *
 * @param x
 * @param y
 */
#define CONCAT2_(x,y) x ## y
/**
 * @brief Concatenate three tokens
 *
 * @param x
 * @param y
 * @param z
 */
#define CONCAT3_(x,y,z) x ## y ## z
/**
 * @brief Concatenate four tokens
 *
 * @param w
 * @param x
 * @param y
 * @param z
 */
#define CONCAT4_(w,x,y,z) w ## x ## y ## z

/**
 * @brief Create PCR register from port name and bit number
 *
 * @param port Port name e.g. A
 * @param num  Bit number e.g. 3
 */
#define PCR(port,num)          CONCAT2_(PORT,port)->PCR[num]

/**
 * @brief Create GPIO register from port name
 *
 * @param port Port name e.g. A => GPIOA
 */
#define GPIO(port)             CONCAT2_(GPIO,port)

/**
 * @brief Create PDOR register from port name
 *
 * @param port Port name e.g. A => GPIOA->PDOR
 */
#define PDOR(port)             CONCAT2_(GPIO,port)->PDOR
/**
 * @brief Create PSOR register from port name
 *
 * @param port Port name e.g. A => GPIOA->PSOR
 */
#define PSOR(port)             CONCAT2_(GPIO,port)->PSOR
/**
 * @brief Create PCOR register from port name
 *
 * @param port Port name e.g. A => GPIOA->PCOR
 */
#define PCOR(port)             CONCAT2_(GPIO,port)->PCOR
/**
 * @brief Create PTOR register from port name
 *
 * @param port Port name e.g. A => GPIOA-PTOR
 */
#define PTOR(port)             CONCAT2_(GPIO,port)->PTOR
/**
 * @brief Create PDIR register from port name
 *
 * @param port Port name e.g. A => GPIOA->PDIR
 */
#define PDIR(port)             CONCAT2_(GPIO,port)->PDIR
/**
 * @brief Create PDDR register from port name
 *
 * @param port Port name e.g. A => GPIOA->PDDR
 */
#define PDDR(port)             CONCAT2_(GPIO,port)->PDDR
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
